solicamb/main/object_oriented_peripheral_interphace/docs/api/class_member_variables.md

# Class Member Variables

## b

* **beginMeasurementYet** ([**Master**](class_master.md))

## c

* **ChipSelect** ([**Communicative**](class_communicative.md))
* **CommsModule** ([**DataSource**](class_data_source.md), [**Identifiable**](class_identifiable.md), [**Instructable**](class_instructable.md), [**Instructor**](class_instructor.md))
* **CurrentData** ([**DataSource**](class_data_source.md))
* **CurrentCommand** ([**Instructor**](class_instructor.md))
* **CurrentRequest** ([**Master**](class_master.md))

## d

* **DataPoints** ([**Data**](struct_data.md))

## f

* **fParams** ([**UserInstructions**](struct_user_instructions.md))
* **fParam** ([**mCmd**](structm_cmd.md), [**sCmd**](structs_cmd.md))

## i

* **InstructionCounter** ([**UserInstructions**](struct_user_instructions.md))
* **InstructionSet** ([**UserInstructions**](struct_user_instructions.md))
* **iParams** ([**UserInstructions**](struct_user_instructions.md))
* **Instruction** ([**mCmd**](structm_cmd.md), [**sCmd**](structs_cmd.md))
* **iParam** ([**mCmd**](structm_cmd.md), [**sCmd**](structs_cmd.md))

## m

* **MeasurementData** ([**Master**](class_master.md))
* **MasterInstructionSet** ([**UserInstructions**](struct_user_instructions.md))

## n

* **NumColumns** ([**Data**](struct_data.md))
* **NumRows** ([**Data**](struct_data.md))
* **NumOfInstructions** ([**UserInstructions**](struct_user_instructions.md))

## r

* **RowHeadings** ([**Data**](struct_data.md))
* **rowUnits** ([**Data**](struct_data.md))

## s

* **SensorName** ([**Identity**](struct_identity.md))
* **sensorChipSelect** ([**Identity**](struct_identity.md))
* **sensorID** ([**Identity**](struct_identity.md))
* **sParam** ([**sCmd**](structs_cmd.md))

## t

* **ThisSensor** ([**Identifiable**](class_identifiable.md))
* **ThisSensorID** ([**Master**](class_master.md))

## u

* **UserInstructionSet** ([**Master**](class_master.md))
