solicamb/main/object_oriented_peripheral_interphace/docs/api/files.md

# File List

Here is a list of all files with brief descriptions:

* **file** [**Communicative.cpp**](_communicative_8cpp.md)   
* **file** [**Communicative.h**](_communicative_8h.md)   
* **file** [**DataSource.cpp**](_data_source_8cpp.md) 
* **file** [**DataSource.h**](_data_source_8h.md)   
* **file** [**Identifiable.cpp**](_identifiable_8cpp.md) 
* **file** [**Identifiable.h**](_identifiable_8h.md)   
* **file** [**Instructable.cpp**](_instructable_8cpp.md) 
* **file** [**Instructable.h**](_instructable_8h.md)   
* **file** [**Instructor.cpp**](_instructor_8cpp.md) 
* **file** [**Instructor.h**](_instructor_8h.md)   
* **file** [**Master.cpp**](_master_8cpp.md)   
* **file** [**Master.h**](_master_8h.md)   
* **file** [**SPI\_InstructionSet.h**](_s_p_i___instruction_set_8h.md)   
* **file** [**Sensor.cpp**](_sensor_8cpp.md) 
* **file** [**Sensor.h**](_sensor_8h.md)   
* **file** [**api.md**](api_8md.md) 
* **file** [**mpi-%s.md**](mpi-_06s_8md.md)
