solicamb/main/object_oriented_peripheral_interphace/docs/api/functions.md

# Functions

## r

* **RequestHandler** ([**Master.h**](_master_8h.md))

## s

* **SPI\_IRQ** ([**Master.cpp**](_master_8cpp.md), [**Master.h**](_master_8h.md))
