solicamb/main/object_oriented_peripheral_interphace/docs/api/variables.md

# Variables

## d

* **DATA\_ROW\_LENGTH** ([**SPI\_InstructionSet.h**](_s_p_i___instruction_set_8h.md))

## i

* **IDENTITY\_SENSOR\_NAME\_LENGTH** ([**SPI\_InstructionSet.h**](_s_p_i___instruction_set_8h.md))

## m

* **MAX\_USER\_INSTRUCTION\_NUMBER** ([**Master.h**](_master_8h.md))
* **MeasurementVectors** ([**SPI\_InstructionSet.h**](_s_p_i___instruction_set_8h.md))
* **mInstruct** ([**SPI\_InstructionSet.h**](_s_p_i___instruction_set_8h.md))

## n

* **NUMBER\_OF\_DATA\_ROWS** ([**SPI\_InstructionSet.h**](_s_p_i___instruction_set_8h.md))

## r

* **REQUEST\_DELAY\_MICROS** ([**Communicative.cpp**](_communicative_8cpp.md))
* **ROW\_HEADING\_LENGTH** ([**SPI\_InstructionSet.h**](_s_p_i___instruction_set_8h.md))
* **ROW\_UNIT\_LENGTH** ([**SPI\_InstructionSet.h**](_s_p_i___instruction_set_8h.md))

## s

* **SensorMaster** ([**Master.cpp**](_master_8cpp.md), [**Master.h**](_master_8h.md))
* **SLAVE\_COMMMAND\_STRING\_LENGTH** ([**SPI\_InstructionSet.h**](_s_p_i___instruction_set_8h.md))
* **sInstruct** ([**SPI\_InstructionSet.h**](_s_p_i___instruction_set_8h.md))
