solicamb/main/object_oriented_peripheral_interphace/temp/latex/hierarchy.tex

\section{Class Hierarchy}
This inheritance list is sorted roughly, but not completely, alphabetically\+:\begin{DoxyCompactList}
\item \contentsline{section}{Communicative}{\pageref{class_communicative}}{}
\item \contentsline{section}{Data}{\pageref{struct_data}}{}
\item \contentsline{section}{Data\+Source}{\pageref{class_data_source}}{}
\begin{DoxyCompactList}
\item \contentsline{section}{Sensor}{\pageref{class_sensor}}{}
\end{DoxyCompactList}
\item \contentsline{section}{Identifiable}{\pageref{class_identifiable}}{}
\begin{DoxyCompactList}
\item \contentsline{section}{Sensor}{\pageref{class_sensor}}{}
\end{DoxyCompactList}
\item \contentsline{section}{Identity}{\pageref{struct_identity}}{}
\item \contentsline{section}{Instructable}{\pageref{class_instructable}}{}
\begin{DoxyCompactList}
\item \contentsline{section}{Sensor}{\pageref{class_sensor}}{}
\end{DoxyCompactList}
\item \contentsline{section}{Instructor}{\pageref{class_instructor}}{}
\begin{DoxyCompactList}
\item \contentsline{section}{Sensor}{\pageref{class_sensor}}{}
\end{DoxyCompactList}
\item \contentsline{section}{Master}{\pageref{class_master}}{}
\item \contentsline{section}{m\+Cmd}{\pageref{structm_cmd}}{}
\item \contentsline{section}{s\+Cmd}{\pageref{structs_cmd}}{}
\item \contentsline{section}{User\+Instructions}{\pageref{struct_user_instructions}}{}
\end{DoxyCompactList}
