solicamb/main/object_oriented_peripheral_interphace/temp/html/_communicative_8cpp__incl.png

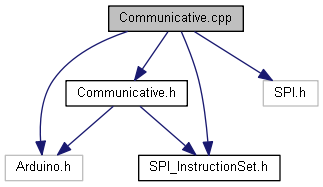
object_oriented_peripheral_interphace/temp/html/_communicative_8cpp__incl.png
