solicamb/main/object_oriented_peripheral_interphace/temp/html/_data_source_8cpp__incl.png

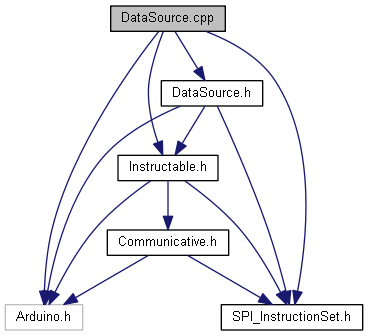
object_oriented_peripheral_interphace/temp/html/_data_source_8cpp__incl.png
