solicamb/main/object_oriented_peripheral_interphace/temp/html/_identifiable_8h__incl.png

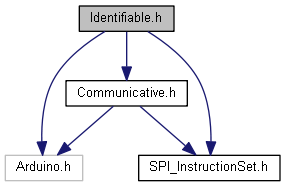
object_oriented_peripheral_interphace/temp/html/_identifiable_8h__incl.png
