solicamb/main/object_oriented_peripheral_interphace/temp/html/_master_8cpp_a8858b26518a9d5c7399f8fd6c12b7633_cgraph.png

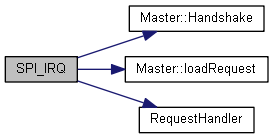
object_oriented_peripheral_interphace/temp/html/_master_8cpp_a8858b26518a9d5c7399f8fd6c12b7633_cgraph.png
