solicamb/main/object_oriented_peripheral_interphace/temp/html/_sensor_8h__incl.png

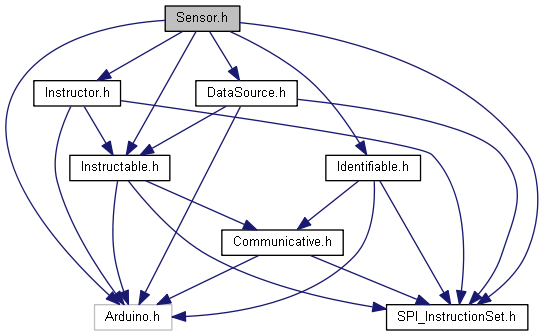
object_oriented_peripheral_interphace/temp/html/_sensor_8h__incl.png
