solicamb/main/object_oriented_peripheral_interphace/temp/html/class_communicative_a4fe112ad5a3d693e39ae44dd43eaf0c1_icgraph.png

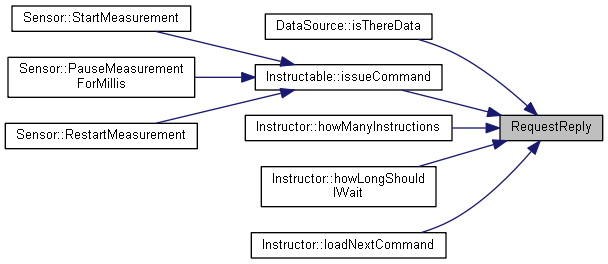
object_oriented_peripheral_interphace/temp/html/class_communicative_a4fe112ad5a3d693e39ae44dd43eaf0c1_icgraph.png
