solicamb/main/object_oriented_peripheral_interphace/temp/html/class_master_a5af38dc77ec10af275ed892e756aee64_cgraph.png

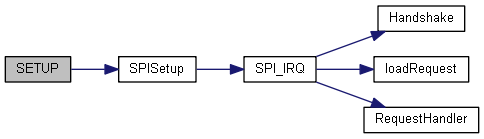
object_oriented_peripheral_interphace/temp/html/class_master_a5af38dc77ec10af275ed892e756aee64_cgraph.png
