solicamb/main/object_oriented_peripheral_interphace/temp/html/class_master_a7d0570bae901dbbd7c88db131fea03c5_icgraph.png

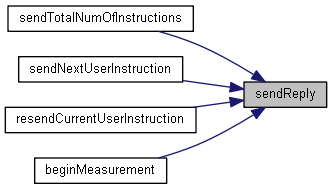
object_oriented_peripheral_interphace/temp/html/class_master_a7d0570bae901dbbd7c88db131fea03c5_icgraph.png
