solicamb/main/object_oriented_peripheral_interphace/temp/html/class_master_a23aca637cd51c40ae469a9ee48725edf_cgraph.png

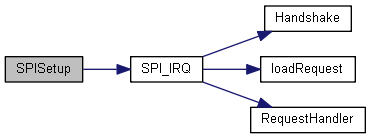
object_oriented_peripheral_interphace/temp/html/class_master_a23aca637cd51c40ae469a9ee48725edf_cgraph.png
