solicamb/main/object_oriented_peripheral_interphace/temp/html/inherit_graph_3.png

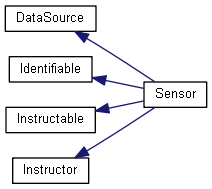
object_oriented_peripheral_interphace/temp/html/inherit_graph_3.png
