solicamb/main/object_oriented_peripheral_interphace/temp/html/solicamb.PNG

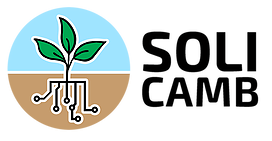
object_oriented_peripheral_interphace/temp/html/solicamb.PNG
