solicamb/main/object_oriented_peripheral_interphace/Pseudo-Unit Tests/Master_Sketch/SPI_Anything.h

#include <Arduino.h>

byte transferAndWait (const byte what)
{
  byte a = SPI.transfer (what);
  delayMicroseconds (20);
  return a;
} // end of transferAndWait


template <typename T> unsigned int SPI_writeAnything (const T& value)
  {
    const byte * p = (const byte*) &value;
    unsigned int i;
    for (i = 0; i < sizeof value; i++)
          transferAndWait(*p++);
    return i;
  }  // end of SPI_writeAnything

template <typename T> unsigned int SPI_readAnything(T& value)
  {
    byte * p = (byte*) &value;
    unsigned int i;
    for (i = 0; i < sizeof value; i++)
          *p++ = transferAndWait (0);
    return i;
  }  // end of SPI_readAnything
  
  
template <typename T> unsigned int SPI_readAnything_ISR(T& value)
  {
    byte * p = (byte*) &value;
    unsigned int i;
    *p++ = SPDR;  // get first byte
    for (i = 1; i < sizeof value; i++)
          *p++ = transferAndWait (0);
    return i;
  }  // end of SPI_readAnything_ISR  

typedef enum sInstruct{
  DisplayInstructionAndWait,
  DisplayInstructionAndWaitForUser,
  DontDisplayAndWait,
  DontDisplayAndContinue,
  ACK,
  Yes,
  No,
  NAK,
  ReferToInt,
  ReferToFloat,
  ReferToString
};

typedef enum mInstruct{
  PauseMeasurementForiParam,
  RestartMeasurementProcedure,
  ResetDevice,
  HowManyInstructions,
  NextCommandPlease,
  IsThereData,
  SendDataPlease,
  WhoAreYou,
  HowLongShouldIWait,
  BeginMeasurement,
  SitRep
};

typedef struct sCmd{
  sInstruct Instruction; 
  char sParam[128];
  int iParam;
  float fParam;
};

typedef struct mCmd{
  mInstruct Instruction;
  int iParam;
  float fParam;
};

typedef struct Identity{
  int namelength;
  char SensorName[50];
  int sensorID;
  int sensorChipSelect;
};

typedef struct Data{
  uint8_t NumColumns;
  uint8_t NumRows;
  char RowHeadings[3][20];
  char rowUnits[3][5];
  float DataPoints[3][128];
};
